HackerspaceAndThe5Pis/course/assets/raspbian/2.1 MicroSD-to-USB converter.jpg

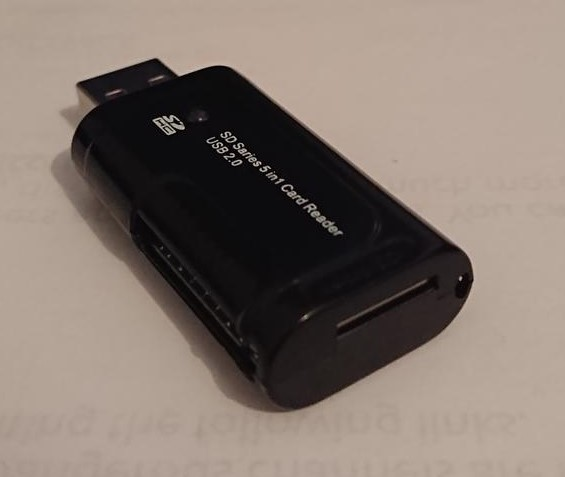
assets/raspbian/2.1 MicroSD-to-USB converter.jpg
