HackerspaceAndThe5Pis/course/assets/raspbian/2.2 RPiLoginPrompt.jpg

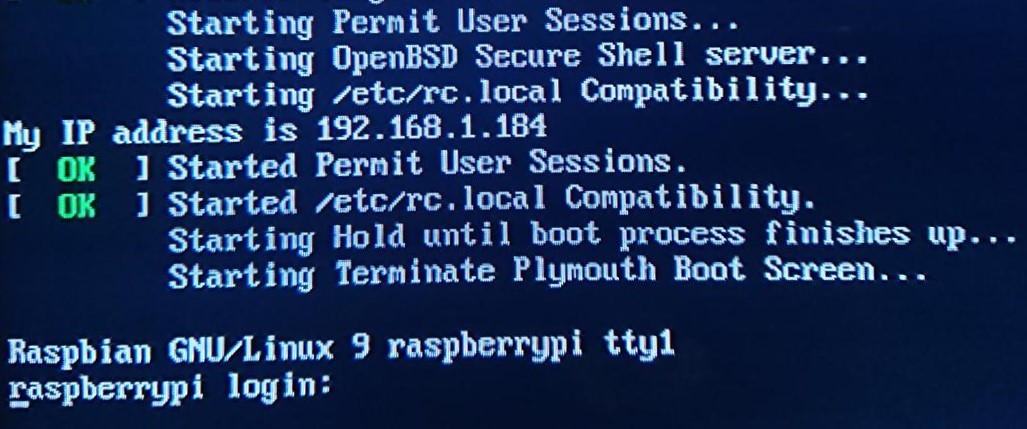
assets/raspbian/2.2 RPiLoginPrompt.jpg
