HackerspaceAndThe5Pis/course/assets/raspbian/2.3 Option8-UpdateToolMenuOption.png

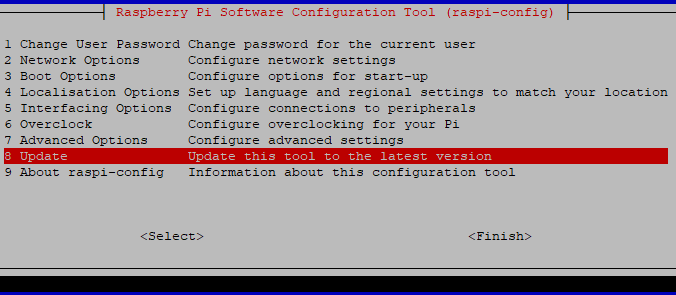
assets/raspbian/2.3 Option8-UpdateToolMenuOption.png
