HackerspaceAndThe5Pis/course/assets/raspbian/2.4 Option2-NetworkMenuOption.png

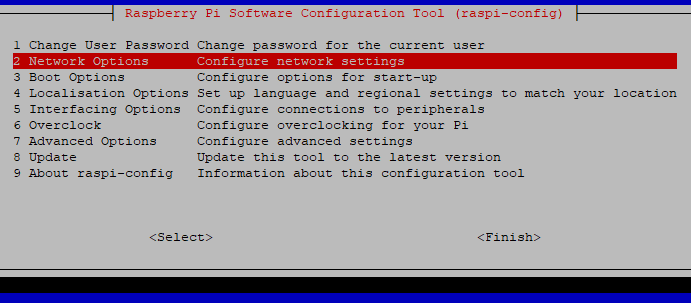
assets/raspbian/2.4 Option2-NetworkMenuOption.png
