HackerspaceAndThe5Pis/course/assets/raspbian/2.5 Option4-LocalisationMenuOption.png

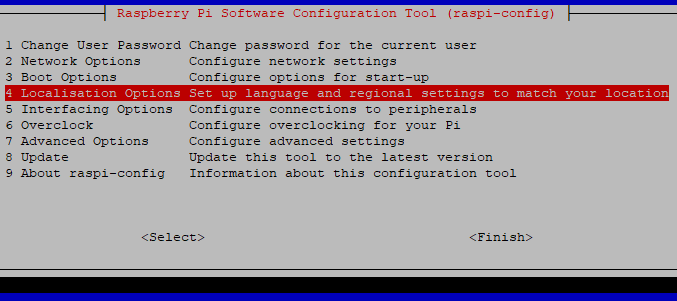
assets/raspbian/2.5 Option4-LocalisationMenuOption.png
