HackerspaceAndThe5Pis/course/assets/raspbian/2.6 Option4-Localisation-Timezone.png

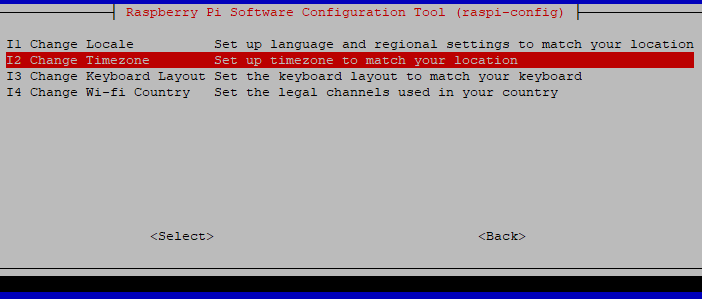
assets/raspbian/2.6 Option4-Localisation-Timezone.png
