HackerspaceAndThe5Pis/course/assets/raspbian/2.7 Option4-Localisation-WifiCountry.png

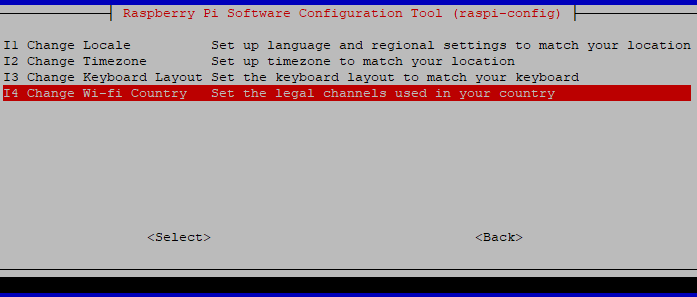
assets/raspbian/2.7 Option4-Localisation-WifiCountry.png
