HackerspaceAndThe5Pis/course/assets/raspbian/2.8 Option7-AdvancedOptions.png

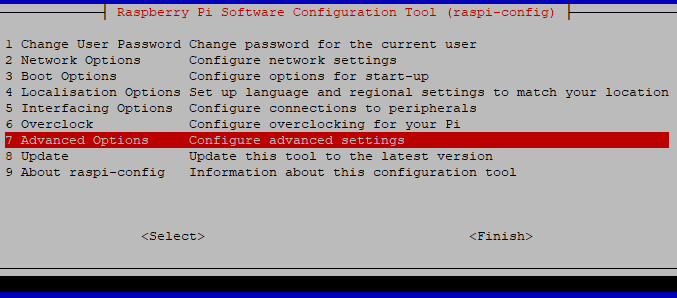
assets/raspbian/2.8 Option7-AdvancedOptions.png
