HackerspaceAndThe5Pis/course/assets/raspbian/2.9 Option7-AdvancedOptions-ExpandFilesystem.png

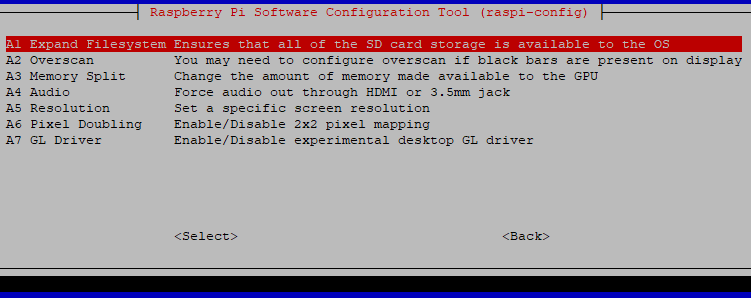
assets/raspbian/2.9 Option7-AdvancedOptions-ExpandFilesystem.png
