HackerspaceAndThe5Pis/course/assets/raspbian/2.10 FilesystemExpanded-CheckSpace.png

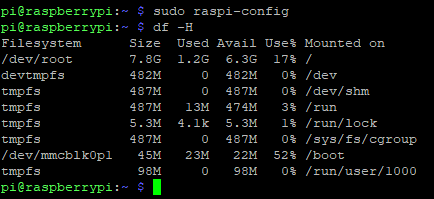
assets/raspbian/2.10 FilesystemExpanded-CheckSpace.png
