HackerspaceAndThe5Pis/course/assets/raspbian/3.2-Download-latest-libsdl-mercurial.png

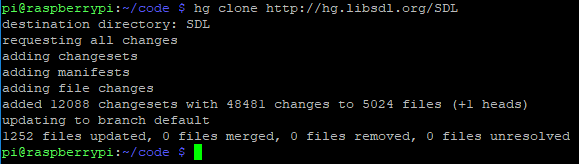
assets/raspbian/3.2-Download-latest-libsdl-mercurial.png
