HackerspaceAndThe5Pis/course/assets/raspbian/5.1-RPiBCMpinLayout-Connections.png

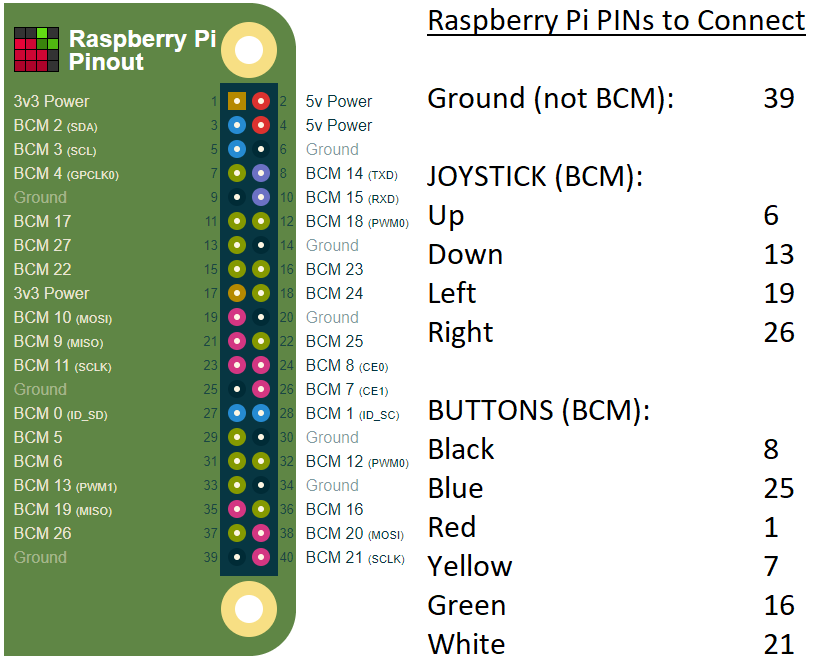
assets/raspbian/5.1-RPiBCMpinLayout-Connections.png
