HackerspaceAndThe5Pis/course/docs/assets/img/about-bg.jpg

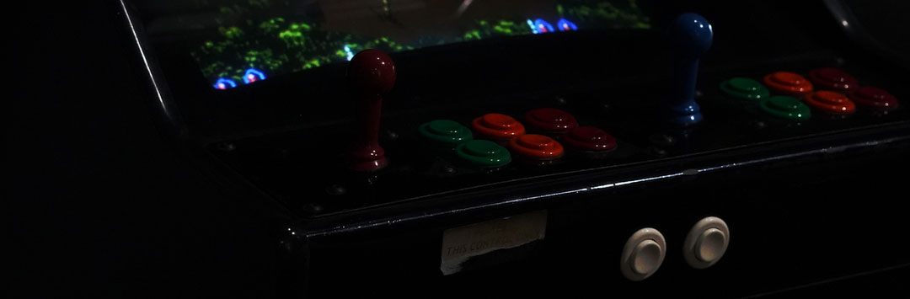
docs/assets/img/about-bg.jpg
