HackerspaceAndThe5Pis/course/docs/assets/img/cad/1.cad-model.png

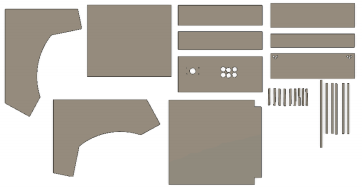
docs/assets/img/cad/1.cad-model.png
