HackerspaceAndThe5Pis/course/docs/assets/img/cad/2.1.cam-workspace.png

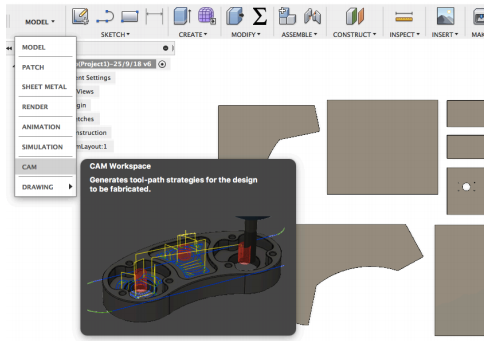
docs/assets/img/cad/2.1.cam-workspace.png
