HackerspaceAndThe5Pis/course/docs/assets/img/cad/2.2.cam-workspace.png

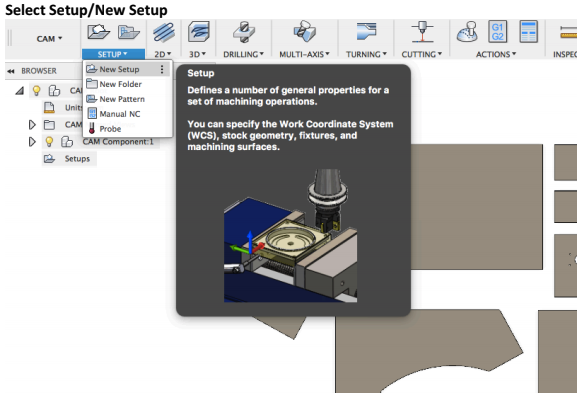
docs/assets/img/cad/2.2.cam-workspace.png
