HackerspaceAndThe5Pis/course/docs/assets/img/cad/2.3.stock-tab.png

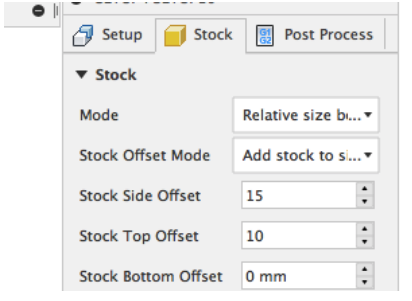
docs/assets/img/cad/2.3.stock-tab.png
