HackerspaceAndThe5Pis/course/docs/assets/img/cad/2.4.orient-the-stock.png

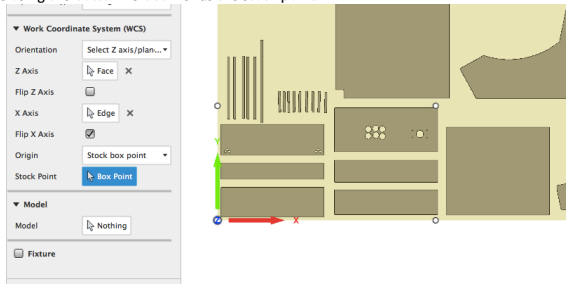
docs/assets/img/cad/2.4.orient-the-stock.png
