HackerspaceAndThe5Pis/course/docs/assets/img/cad/2.5.add-our-tool.png

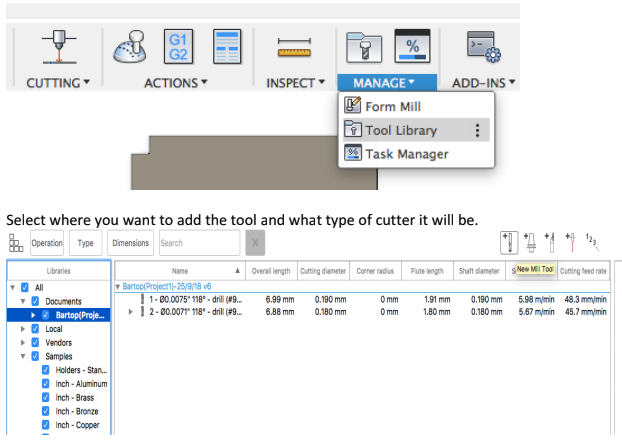
docs/assets/img/cad/2.5.add-our-tool.png
