HackerspaceAndThe5Pis/course/docs/assets/img/cad/2.5.spped-and-feed.png

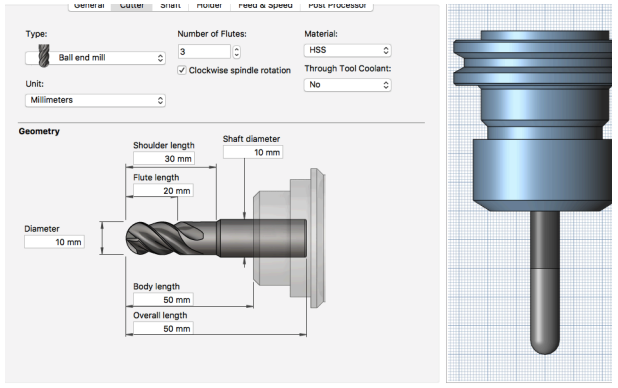
docs/assets/img/cad/2.5.spped-and-feed.png
