HackerspaceAndThe5Pis/course/docs/assets/img/cad/2.6.tool-path-6.png

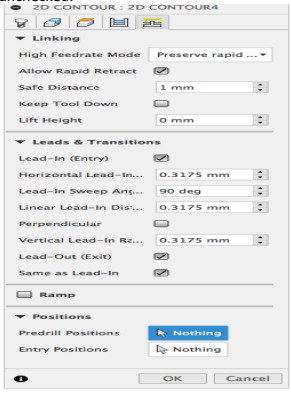
docs/assets/img/cad/2.6.tool-path-6.png
