HackerspaceAndThe5Pis/course/docs/assets/img/cad/2.7.generic-posts.png

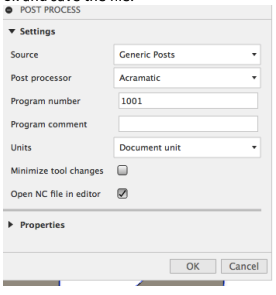
docs/assets/img/cad/2.7.generic-posts.png
