HackerspaceAndThe5Pis/course/docs/assets/img/cad/2.7.machine-control-software.png

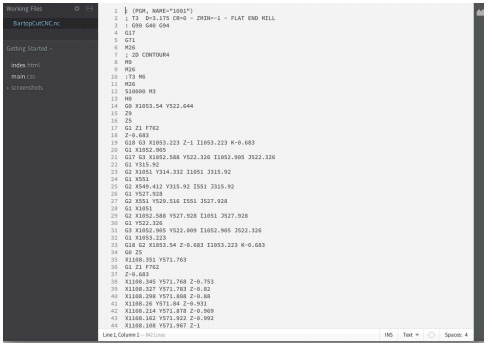
docs/assets/img/cad/2.7.machine-control-software.png
