HackerspaceAndThe5Pis/course/docs/assets/img/cad/2.7.output-gcode.png

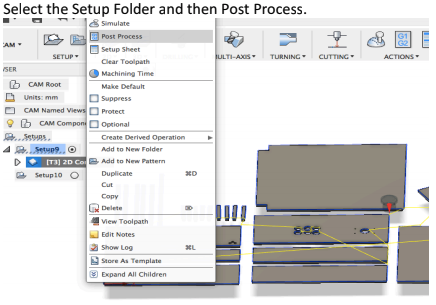
docs/assets/img/cad/2.7.output-gcode.png
