HackerspaceAndThe5Pis/course/docs/assets/img/cnc/1.required-pieces.png

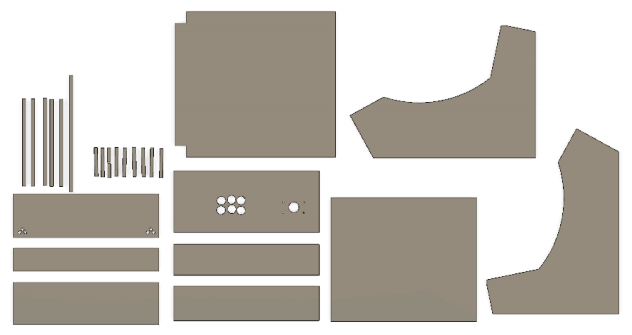
docs/assets/img/cnc/1.required-pieces.png
