HackerspaceAndThe5Pis/course/docs/assets/img/cnc/2.required-pieces-2.png

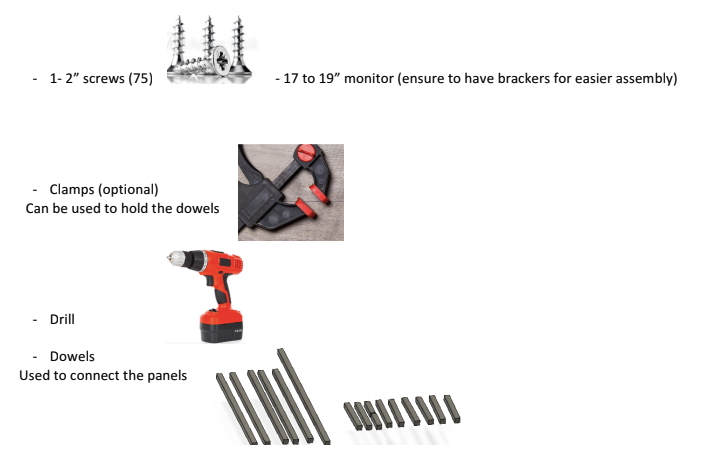
docs/assets/img/cnc/2.required-pieces-2.png
