HackerspaceAndThe5Pis/course/docs/assets/img/cnc/3.side-bottom-panel.png

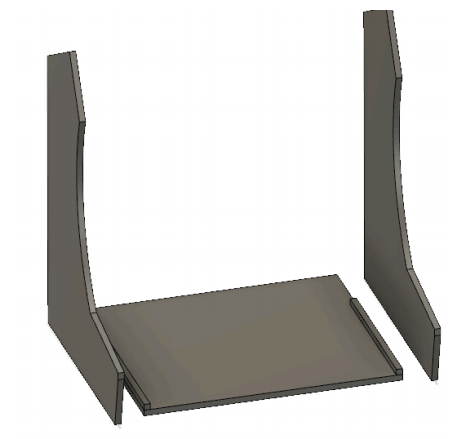
docs/assets/img/cnc/3.side-bottom-panel.png
