HackerspaceAndThe5Pis/course/docs/assets/img/cnc/5.bottom-base-panel.png

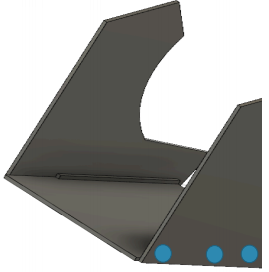
docs/assets/img/cnc/5.bottom-base-panel.png
