HackerspaceAndThe5Pis/course/docs/assets/img/cnc/6.attached-panel.png

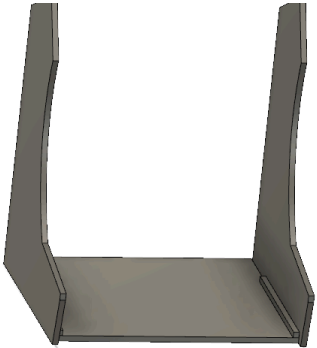
docs/assets/img/cnc/6.attached-panel.png
