HackerspaceAndThe5Pis/course/docs/assets/img/cnc/7.main-and-lower-control-panel.png

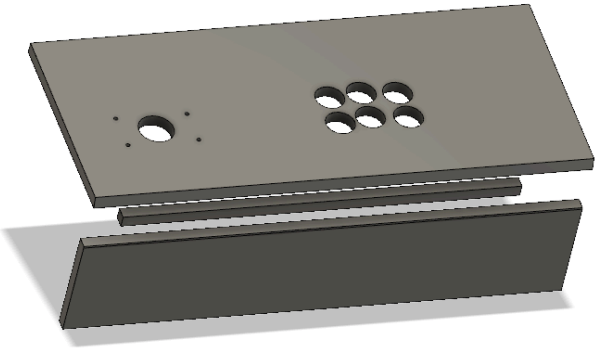
docs/assets/img/cnc/7.main-and-lower-control-panel.png
