HackerspaceAndThe5Pis/course/docs/assets/img/cnc/8.dowels-control-panel.png

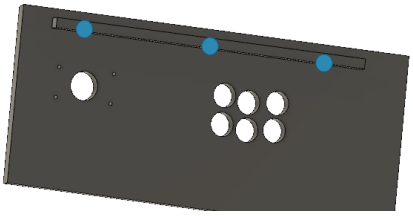
docs/assets/img/cnc/8.dowels-control-panel.png
