HackerspaceAndThe5Pis/course/docs/assets/img/cnc/9.dowels-control-panel.png

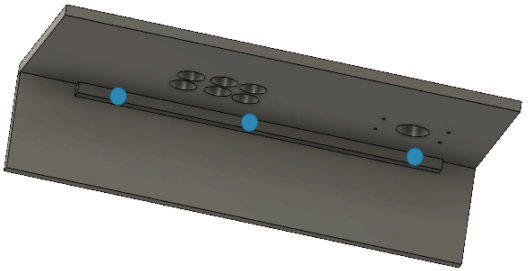
docs/assets/img/cnc/9.dowels-control-panel.png
