HackerspaceAndThe5Pis/course/docs/assets/img/cnc/10.controller-panel.png

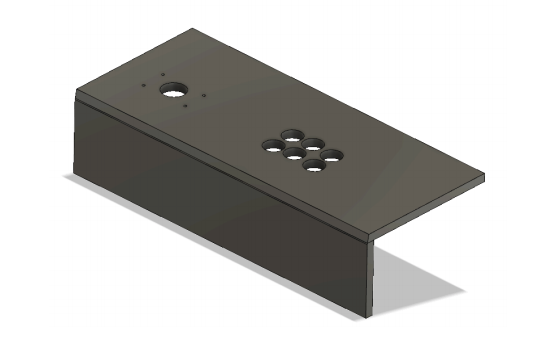
docs/assets/img/cnc/10.controller-panel.png
