HackerspaceAndThe5Pis/course/docs/assets/img/cnc/11.control-panel-attach.png

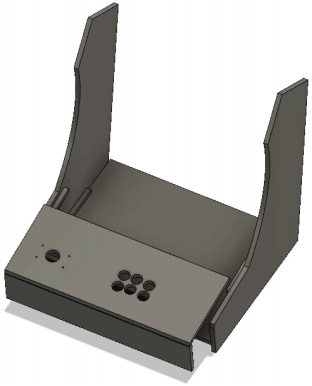
docs/assets/img/cnc/11.control-panel-attach.png
