HackerspaceAndThe5Pis/course/docs/assets/img/cnc/13.control-panel-attached.png

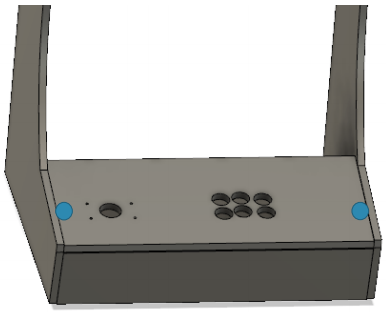
docs/assets/img/cnc/13.control-panel-attached.png
