HackerspaceAndThe5Pis/course/docs/assets/img/cnc/17.monitor-support.png

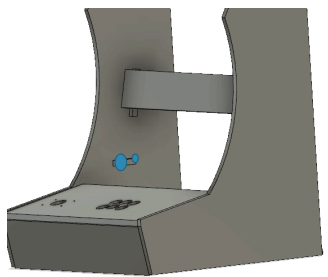
docs/assets/img/cnc/17.monitor-support.png
