HackerspaceAndThe5Pis/course/docs/assets/img/cnc/18.monitor-board.png

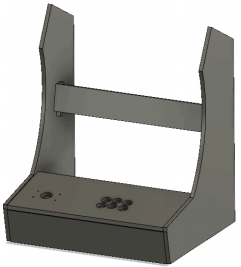
docs/assets/img/cnc/18.monitor-board.png
