HackerspaceAndThe5Pis/course/docs/assets/img/cnc/19.mounting-back-panel.png

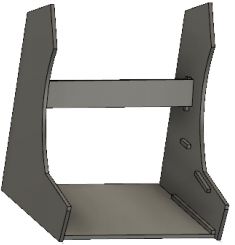
docs/assets/img/cnc/19.mounting-back-panel.png
