HackerspaceAndThe5Pis/course/docs/assets/img/cnc/20.mounting-back-panel.png

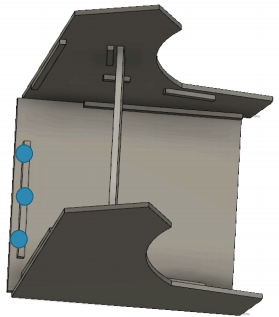
docs/assets/img/cnc/20.mounting-back-panel.png
