HackerspaceAndThe5Pis/course/docs/assets/img/cnc/22.back-panel-attached.png

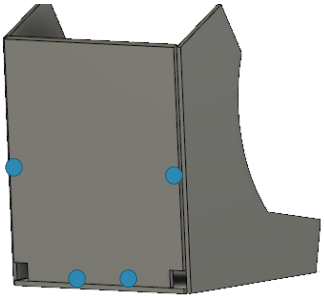
docs/assets/img/cnc/22.back-panel-attached.png
