HackerspaceAndThe5Pis/course/docs/assets/img/cnc/23.top-panel.png

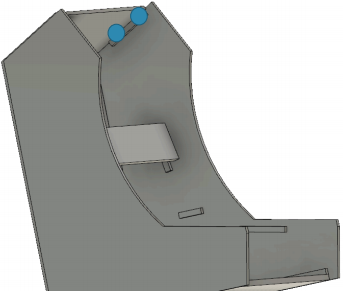
docs/assets/img/cnc/23.top-panel.png
