HackerspaceAndThe5Pis/course/docs/assets/img/cnc/24.top-panel-attached.png

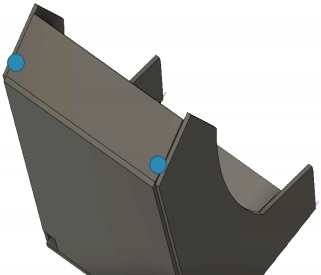
docs/assets/img/cnc/24.top-panel-attached.png
