HackerspaceAndThe5Pis/course/docs/assets/img/cnc/25.speaker-panel-attach.png

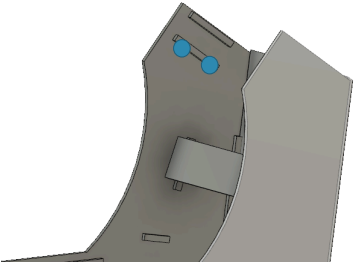
docs/assets/img/cnc/25.speaker-panel-attach.png
