HackerspaceAndThe5Pis/course/docs/assets/img/cnc/28.reattach-panel.png

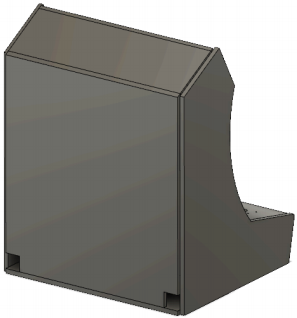
docs/assets/img/cnc/28.reattach-panel.png
