HackerspaceAndThe5Pis/course/docs/assets/img/cnc/29.reattach-panel.png

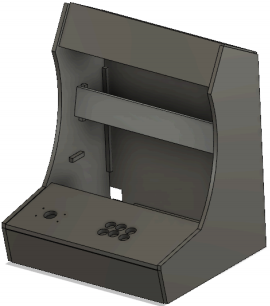
docs/assets/img/cnc/29.reattach-panel.png
