HackerspaceAndThe5Pis/course/docs/assets/img/cnc/30.plexiglass.png

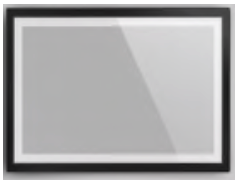
docs/assets/img/cnc/30.plexiglass.png
