HackerspaceAndThe5Pis/course/docs/assets/img/course_bg.jpg

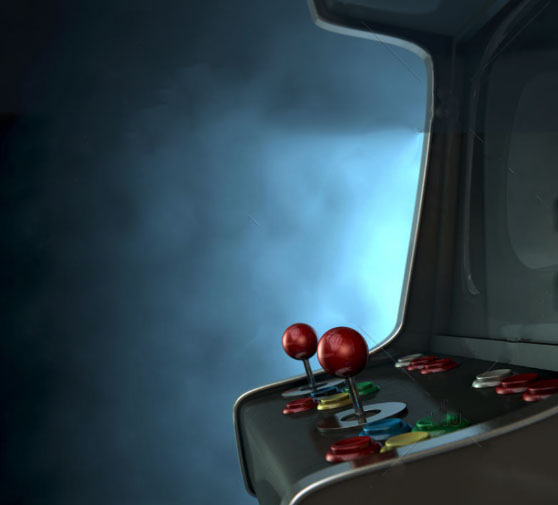
docs/assets/img/course_bg.jpg
