HackerspaceAndThe5Pis/course/docs/assets/img/teams/berkay.png

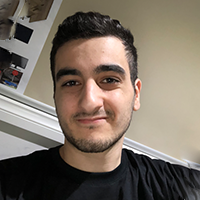
docs/assets/img/teams/berkay.png
