HackerspaceAndThe5Pis/course/docs/assets/img/teams/luke.jpg

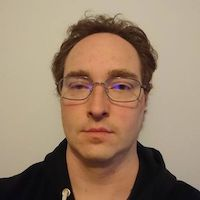
docs/assets/img/teams/luke.jpg
