HackerspaceAndThe5Pis/course/docs/assets/img/teams/riley.png

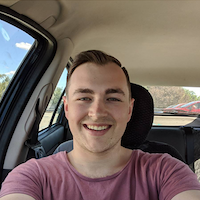
docs/assets/img/teams/riley.png
