HackerspaceAndThe5Pis/course/docs/assets/img/cnc/12.install-dowels-side-panel.png

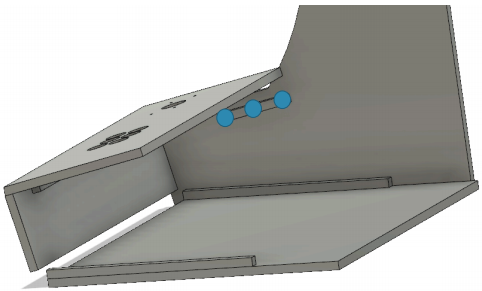
docs/assets/img/cnc/12.install-dowels-side-panel.png
