HackerspaceAndThe5Pis/course/docs/assets/img/cnc/21.install-dowels-side-panel.png

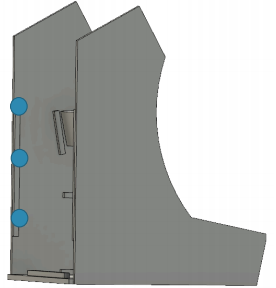
docs/assets/img/cnc/21.install-dowels-side-panel.png
