HackerspaceAndThe5Pis/course/docs/assets/img/measurements/1.button-side.jpg

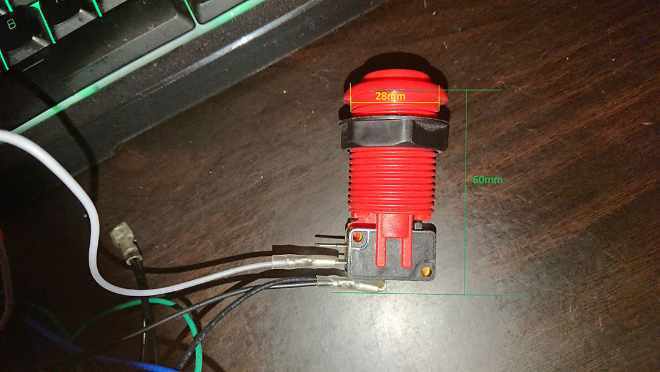
docs/assets/img/measurements/1.button-side.jpg
