HackerspaceAndThe5Pis/course/docs/assets/img/measurements/3.joystick-bottom.jpg

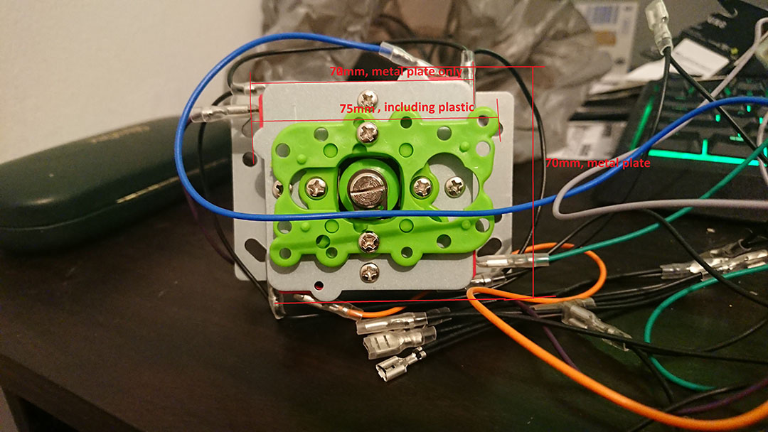
docs/assets/img/measurements/3.joystick-bottom.jpg
