HackerspaceAndThe5Pis/course/docs/assets/img/measurements/4.joystick-long-side.jpg

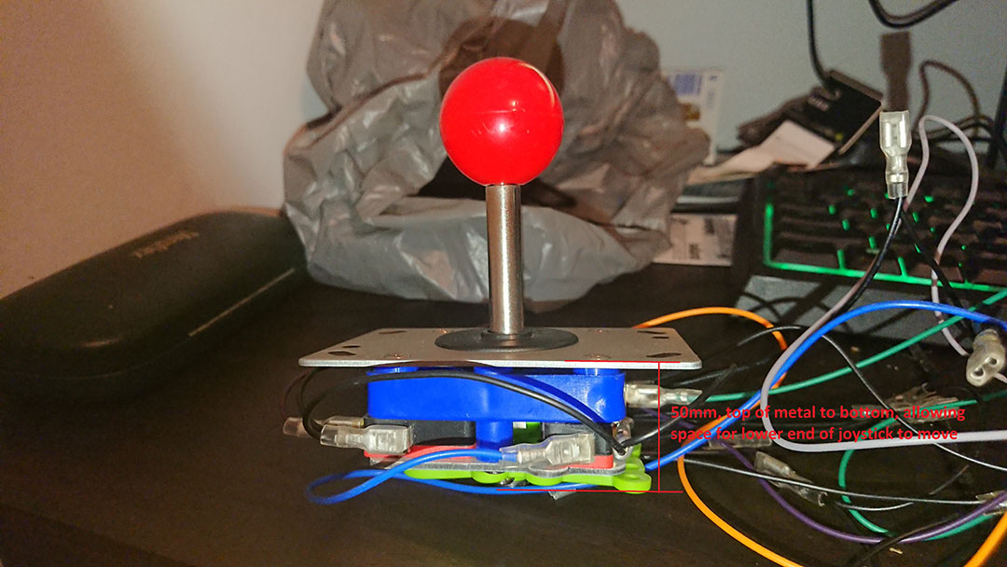
docs/assets/img/measurements/4.joystick-long-side.jpg
