HackerspaceAndThe5Pis/course/docs/assets/img/measurements/5.joystick-top.jpg

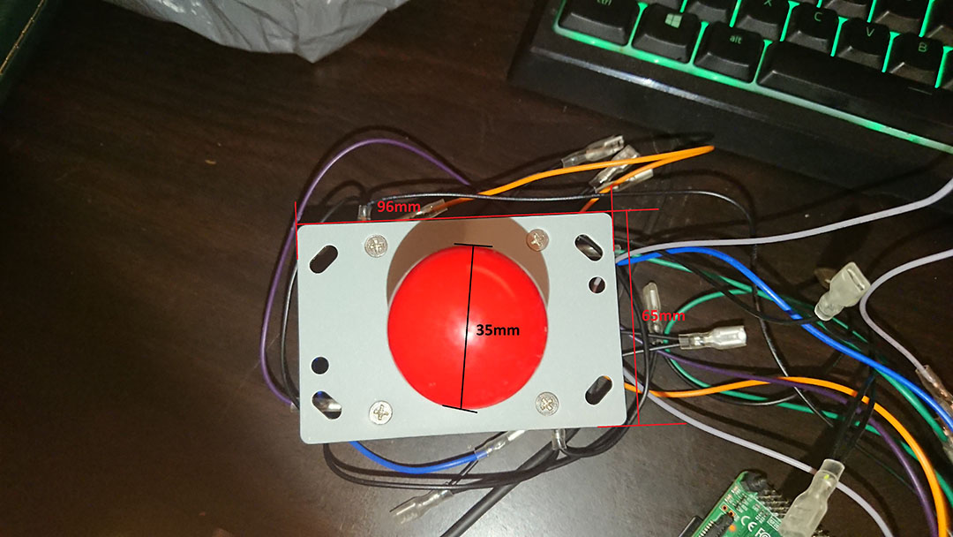
docs/assets/img/measurements/5.joystick-top.jpg
