HackerspaceAndThe5Pis/course/docs/assets/img/measurements/6.raspberry-pi-2-long-side.jpg

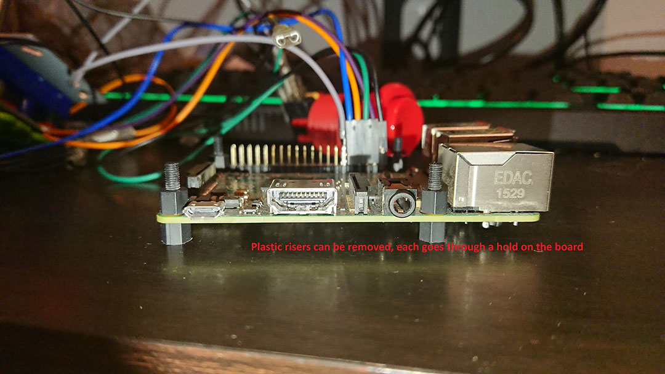
docs/assets/img/measurements/6.raspberry-pi-2-long-side.jpg
