HackerspaceAndThe5Pis/course/docs/assets/img/measurements/7.raspberry-pi-2-short-side.jpg

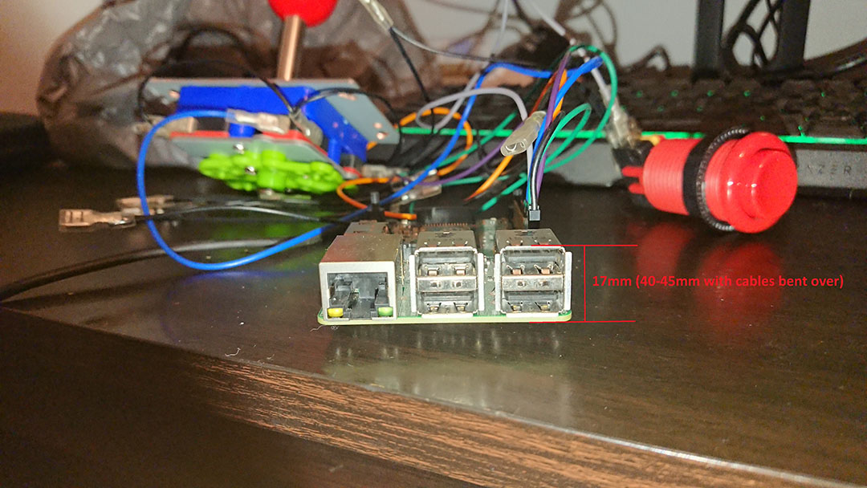
docs/assets/img/measurements/7.raspberry-pi-2-short-side.jpg
