HackerspaceAndThe5Pis/course/docs/assets/img/measurements/8.raspberry-pi-2-top.jpg

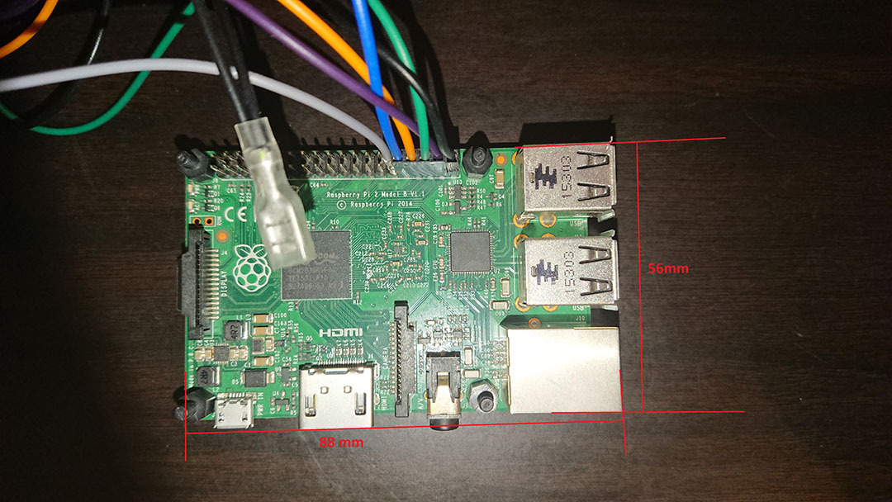
docs/assets/img/measurements/8.raspberry-pi-2-top.jpg
